Staringlizard/memwa2/hw/drivers/disp/disp.c

/*
 * memwa2 display driver
 *
 * Copyright (c) 2016 Mathias Edman <mail@dicetec.com>
 *
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
 */


/**
 * This driver handles all graphics and configuration.
 */

#include "disp.h"
#include "stm32f7xx_hal_ltdc.h"
#include "stm32f7xx_hal_dma2d.h"
#include <string.h>

#define VGA_WIDTH  ((uint16_t)640)
#define VGA_HEIGHT ((uint16_t)480)
#define VGA_HSYNC  ((uint16_t)96)
#define VGA_HBP    ((uint16_t)48)
#define VGA_HFP    ((uint16_t)16)
#define VGA_VSYNC  ((uint16_t)2)
#define VGA_VBP    ((uint16_t)31)
#define VGA_VFP    ((uint16_t)11)

#define SVGA_WIDTH  ((uint16_t)800)
#define SVGA_HEIGHT ((uint16_t)600)
#define SVGA_HSYNC  ((uint16_t)128)
#define SVGA_HBP    ((uint16_t)88)
#define SVGA_HFP    ((uint16_t)40)
#define SVGA_VSYNC  ((uint16_t)4)
#define SVGA_VBP    ((uint16_t)23)
#define SVGA_VFP    ((uint16_t)1)

#define DISP_MAIN_LAYER       0
#define DISP_EMU_LAYER        1

#define CLUT_TEXT_BG_POS      16
#define CLUT_TEXT_FG_POS      17
#define CLUT_MARKER_POS       18
#define CLUT_MAX              19

LTDC_HandleTypeDef g_ltdc_handle; /* used by irq.c */
static LTDC_LayerCfgTypeDef g_ltdc_layer_cfg_a[2];
static uint32_t g_memory_addr_a[3];

static uint32_t clut_a[CLUT_MAX] =
{
    0x000000, /* black */
    0xFFFFFF, /* white */
    0x744335, /* red */
    0x7CACBA, /* cyan */
    0x7B4890, /* violet */
    0x64974F, /* green */
    0x403285, /* blue */
    0xBFCD7A, /* yellow */
    0x7B5B2F, /* orange */
    0x4f4500, /* brown */
    0xa37265, /* light red */
    0x505050, /* grey 1 */
    0x787878, /* grey 2 */
    0xa4d78e, /* light green */
    0x786abd, /* light blue */
    0x9f9f9f, /* grey 3 */
    0x010211, /* text background */
    0x8f9fed, /* text forground */
    0x151bfb, /* marker */
};

void disp_init(disp_mode_t disp_mode)
{
    switch(disp_mode)
    {
        case DISP_MODE_VGA:
            /* Timing configuration */
            g_ltdc_handle.Init.HorizontalSync = (VGA_HSYNC - 1);
            g_ltdc_handle.Init.VerticalSync = (VGA_VSYNC - 1);
            g_ltdc_handle.Init.AccumulatedHBP = (VGA_HSYNC + VGA_HBP - 1);
            g_ltdc_handle.Init.AccumulatedVBP = (VGA_VSYNC + VGA_VBP - 1);  
            g_ltdc_handle.Init.AccumulatedActiveH = (VGA_HEIGHT + VGA_VSYNC + VGA_VBP - 1);
            g_ltdc_handle.Init.AccumulatedActiveW = (VGA_WIDTH + VGA_HSYNC + VGA_HBP - 1);
            g_ltdc_handle.Init.TotalHeigh = (VGA_HEIGHT + VGA_VSYNC + VGA_VBP + VGA_VFP - 1);
            g_ltdc_handle.Init.TotalWidth = (VGA_WIDTH + VGA_HSYNC + VGA_HBP + VGA_HFP - 1);

            /* Background value */
            g_ltdc_handle.Init.Backcolor.Blue = 0;
            g_ltdc_handle.Init.Backcolor.Green = 0;
            g_ltdc_handle.Init.Backcolor.Red = 0;

            /* Polarity */
            g_ltdc_handle.Init.HSPolarity = LTDC_HSPOLARITY_AL;
            g_ltdc_handle.Init.VSPolarity = LTDC_VSPOLARITY_AL; 
            g_ltdc_handle.Init.DEPolarity = LTDC_DEPOLARITY_AL;  
            g_ltdc_handle.Init.PCPolarity = LTDC_PCPOLARITY_IPC;
            g_ltdc_handle.Instance = LTDC;
            break;
        case DISP_MODE_SVGA:
            /* Timing configuration */
            g_ltdc_handle.Init.HorizontalSync = (SVGA_HSYNC - 1);
            g_ltdc_handle.Init.VerticalSync = (SVGA_VSYNC - 1);
            g_ltdc_handle.Init.AccumulatedHBP = (SVGA_HSYNC + SVGA_HBP - 1);
            g_ltdc_handle.Init.AccumulatedVBP = (SVGA_VSYNC + SVGA_VBP - 1);  
            g_ltdc_handle.Init.AccumulatedActiveH = (SVGA_HEIGHT + SVGA_VSYNC + SVGA_VBP - 1);
            g_ltdc_handle.Init.AccumulatedActiveW = (SVGA_WIDTH + SVGA_HSYNC + SVGA_HBP - 1);
            g_ltdc_handle.Init.TotalHeigh = (SVGA_HEIGHT + SVGA_VSYNC + SVGA_VBP + SVGA_VFP - 1);
            g_ltdc_handle.Init.TotalWidth = (SVGA_WIDTH + SVGA_HSYNC + SVGA_HBP + SVGA_HFP - 1); 

            /* Background value */
            g_ltdc_handle.Init.Backcolor.Blue = 0;
            g_ltdc_handle.Init.Backcolor.Green = 0;
            g_ltdc_handle.Init.Backcolor.Red = 0;

            /* Polarity */
            g_ltdc_handle.Init.HSPolarity = LTDC_HSPOLARITY_AL;
            g_ltdc_handle.Init.VSPolarity = LTDC_VSPOLARITY_AL; 
            g_ltdc_handle.Init.DEPolarity = LTDC_DEPOLARITY_AL;  
            g_ltdc_handle.Init.PCPolarity = LTDC_PCPOLARITY_IIPC;
            g_ltdc_handle.Instance = LTDC;
    }

    HAL_LTDC_Init(&g_ltdc_handle);

    HAL_LTDC_ConfigCLUT(&g_ltdc_handle, clut_a, CLUT_MAX, 0);
    HAL_LTDC_ConfigCLUT(&g_ltdc_handle, clut_a, CLUT_MAX, 1);

    HAL_LTDC_EnableCLUT(&g_ltdc_handle, 0);
    HAL_LTDC_EnableCLUT(&g_ltdc_handle, 1);

    HAL_LTDC_ProgramLineEvent(&g_ltdc_handle, 200);
    __HAL_LTDC_DISABLE_IT(&g_ltdc_handle, LTDC_IT_LI); /* Disable line events for now */
}

void *disp_get_layer(uint8_t layer)
{
    return (void *)(g_ltdc_handle.LayerCfg[layer].FBStartAdress);
}

void disp_set_memory(uint8_t layer, uint32_t memory)
{
    g_memory_addr_a[layer] = memory;
}

void disp_set_layer(uint8_t layer,
                    uint32_t window_x0,
                    uint32_t window_x1,
                    uint32_t window_y0,
                    uint32_t window_y1,
                    uint32_t buffer_x,
                    uint32_t buffer_y,
                    uint8_t alpha,
                    uint32_t pixel_format)
{
    /* Layer Init */
    g_ltdc_layer_cfg_a[layer].WindowX0 = window_x0;
    g_ltdc_layer_cfg_a[layer].WindowX1 = window_x1;
    g_ltdc_layer_cfg_a[layer].WindowY0 = window_y0;
    g_ltdc_layer_cfg_a[layer].WindowY1 = window_y1;
    g_ltdc_layer_cfg_a[layer].Alpha = alpha;
    g_ltdc_layer_cfg_a[layer].Alpha0 = 0;
    g_ltdc_layer_cfg_a[layer].Backcolor.Blue = 0;
    g_ltdc_layer_cfg_a[layer].Backcolor.Green = 0;
    g_ltdc_layer_cfg_a[layer].Backcolor.Red = 0;
    g_ltdc_layer_cfg_a[layer].BlendingFactor1 = LTDC_BLENDING_FACTOR1_PAxCA;
    g_ltdc_layer_cfg_a[layer].BlendingFactor2 = LTDC_BLENDING_FACTOR2_PAxCA;
    g_ltdc_layer_cfg_a[layer].ImageWidth = buffer_x;
    g_ltdc_layer_cfg_a[layer].ImageHeight = buffer_y;
    g_ltdc_layer_cfg_a[layer].PixelFormat = pixel_format;
    g_ltdc_layer_cfg_a[layer].FBStartAdress = g_memory_addr_a[layer];

    HAL_LTDC_ConfigLayer(&g_ltdc_handle, &g_ltdc_layer_cfg_a[layer], layer);
}

void disp_activate_layer(uint8_t layer)
{
    __HAL_LTDC_LAYER_ENABLE(&g_ltdc_handle, layer);
    __HAL_LTDC_RELOAD_CONFIG(&g_ltdc_handle);
}

void disp_deactivate_layer(uint8_t layer)
{
    __HAL_LTDC_LAYER_DISABLE(&g_ltdc_handle, layer);
    __HAL_LTDC_RELOAD_CONFIG(&g_ltdc_handle);
}

void disp_fill_layer(uint8_t layer, uint32_t color)
{
    uint32_t i;

    for(i = 0; i < g_ltdc_layer_cfg_a[layer].ImageWidth * g_ltdc_layer_cfg_a[layer].ImageHeight; i++)
    {
        if(g_ltdc_layer_cfg_a[layer].PixelFormat == LTDC_PIXEL_FORMAT_L8)
        {
            *((uint8_t *)g_ltdc_layer_cfg_a[layer].FBStartAdress + i) = color;
        }
        else if(g_ltdc_layer_cfg_a[layer].PixelFormat == LTDC_PIXEL_FORMAT_RGB565)
        {
            *((uint16_t *)g_ltdc_layer_cfg_a[layer].FBStartAdress + i) = color;
        }
        else if(g_ltdc_layer_cfg_a[layer].PixelFormat == LTDC_PIXEL_FORMAT_ARGB8888)
        {
            *((uint32_t *)g_ltdc_layer_cfg_a[layer].FBStartAdress + i) = color;
        }
    }
}

void disp_move_layer(uint8_t layer, uint32_t x, uint32_t y)
{
    HAL_LTDC_SetWindowPosition(&g_ltdc_handle, x, y, layer);
}

void disp_flip_buffer(uint8_t **done_buffer_pp)
{
    /* Set layer to be displayed */
    HAL_LTDC_SetAddress(&g_ltdc_handle, (uint32_t)*done_buffer_pp, DISP_EMU_LAYER);

    /* And shift buffer */
    if((uint32_t)*done_buffer_pp == g_memory_addr_a[MEM_ADDR_BUFFER1])
    {
        *done_buffer_pp = (uint8_t *)g_memory_addr_a[MEM_ADDR_BUFFER2];
    }
    else
    {
        *done_buffer_pp = (uint8_t *)g_memory_addr_a[MEM_ADDR_BUFFER1];
    }
}

void disp_set_clut_table(uint32_t *clut_p)
{
    memcpy(clut_a, clut_p, CLUT_MAX * sizeof(uint32_t));
    HAL_LTDC_ConfigCLUT(&g_ltdc_handle, clut_a, CLUT_MAX, 0);
    HAL_LTDC_ConfigCLUT(&g_ltdc_handle, clut_a, CLUT_MAX, 1);
}

void disp_enable_clut(uint8_t layer)
{
    HAL_LTDC_EnableCLUT(&g_ltdc_handle, layer);
}

void disp_disable_clut(uint8_t layer)
{
    HAL_LTDC_DisableCLUT(&g_ltdc_handle, layer);
}

void HAL_LTDC_ErrorCallback(LTDC_HandleTypeDef *hltdc)
{
    main_warning("HAL LTDC error!", __FILE__, __LINE__, (uint32_t)hltdc->ErrorCode);
    __HAL_LTDC_ENABLE_IT(hltdc, LTDC_IT_TE);
    __HAL_LTDC_ENABLE_IT(hltdc, LTDC_IT_FU);
    hltdc->State = HAL_LTDC_STATE_READY;
    hltdc->ErrorCode = HAL_LTDC_ERROR_NONE;
}

void HAL_LTDC_LineEvenCallback(LTDC_HandleTypeDef *hltdc)
{
    main_error("HAL LTDC line callback!", __FILE__, __LINE__, (uint32_t)hltdc->ErrorCode);
    //HAL_LTDC_ProgramLineEvent(hltdc, 200);
}
