Staringlizard/memwa2/hw/irq/irq.c

/**
  ******************************************************************************
  * @file    FatFs/FatFs_uSD/Src/stm32f7xx_it.c
  * @author  MCD Application Team
  * @version V1.0.2
  * @date    18-November-2015 
  * @brief   Main Interrupt Service Routines.
  *          This file provides template for all exceptions handler and
  *          peripherals interrupt service routine.
  ******************************************************************************
  * @attention
  *
  * <h2><center>&copy; COPYRIGHT(c) 2015 STMicroelectronics</center></h2>
  *
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
  ******************************************************************************
  */

/* Includes ------------------------------------------------------------------*/
#include "irq.h"
#include "config.h"
#include "usbd_cdc_if.h"
#include "sidbus.h"
#include "joyst.h"
#include "timer.h"
#include "adv7511.h"

/* Private typedef -----------------------------------------------------------*/
/* Private define ------------------------------------------------------------*/
/* Private macro -------------------------------------------------------------*/
/* Private variables ---------------------------------------------------------*/
/* Private function prototypes -----------------------------------------------*/
/* Private functions ---------------------------------------------------------*/

extern HCD_HandleTypeDef hhcd;
extern PCD_HandleTypeDef hpcd;
extern PCD_HandleTypeDef hpcd;
extern LTDC_HandleTypeDef g_ltdc_handle;

/******************************************************************************/
/*            Cortex-M7 Processor Exceptions Handlers                         */
/******************************************************************************/

/**
  * @brief  This function handles NMI exception.
  * @param  None
  * @retval None
  */
void NMI_Handler(void)
{
}

/**
  * @brief  This function handles Hard Fault exception.
  * @param  None
  * @retval None
  */
void HardFault_Handler(void)
{
  /* Go to infinite loop when Hard Fault exception occurs */
  while (1)
  {
  }
}

/**
  * @brief  This function handles Memory Manage exception.
  * @param  None
  * @retval None
  */
void MemManage_Handler(void)
{
  /* Go to infinite loop when Memory Manage exception occurs */
  while (1)
  {
  }
}

/**
  * @brief  This function handles Bus Fault exception.
  * @param  None
  * @retval None
  */
void BusFault_Handler(void)
{
  /* Go to infinite loop when Bus Fault exception occurs */
  while (1)
  {
  }
}

/**
  * @brief  This function handles Usage Fault exception.
  * @param  None
  * @retval None
  */
void UsageFault_Handler(void)
{
  /* Go to infinite loop when Usage Fault exception occurs */
  while (1)
  {
  }
}

/**
  * @brief  This function handles SVCall exception.
  * @param  None
  * @retval None
  */
void SVC_Handler(void)
{
}

/**
  * @brief  This function handles Debug Monitor exception.
  * @param  None
  * @retval None
  */
void DebugMon_Handler(void)
{
}

/**
  * @brief  This function handles PendSVC exception.
  * @param  None
  * @retval None
  */
void PendSV_Handler(void)
{
}

/**
  * @brief  This function handles SysTick Handler.
  * @param  None
  * @retval None
  */
void SysTick_Handler(void)
{
  HAL_IncTick();
  systimer_tick();
}

void TIM3_IRQHandler(void)
{
  timer3_tick();
}

void LTDC_IRQHandler(void)
{
  HAL_LTDC_IRQHandler(&g_ltdc_handle);
}

void LTDC_ER_IRQHandler(void)
{
  HAL_LTDC_IRQHandler(&g_ltdc_handle);
}

/**
  * @brief  This function handles DMA2 Stream 3 interrupt request.
  * @param  None
  * @retval None
  */
void DMA2_Stream3_IRQHandler(void)
{
  ;//SD_DMA_Rx_IRQHandler();
}

/**
  * @brief  This function handles DMA2 Stream 6 interrupt request.
  * @param  None
  * @retval None
  */
void DMA2_Stream6_IRQHandler(void)
{
  ;//SD_DMA_Tx_IRQHandler(); 
}

/**
  * @brief  This function handles SDIO interrupt request.
  * @param  None
  * @retval None
  */
void SDMMC1_IRQHandler(void)
{
  ;//SD_IRQHandler();
}

/**
  * @brief  This function handles PPP interrupt request.
  * @param  None
  * @retval None
  */
/*void PPP_IRQHandler(void)
{
}*/

/**
  * @brief  This function handles USB-On-The-Go FS/HS global interrupt request.
  * @param  None
  * @retval None
  */
void OTG_FS_IRQHandler(void)
{
  HAL_PCD_IRQHandler(&hpcd);

  /* Flush the outgoing printf data */
  CDC_Itf_Flush();
}

/**
  * @brief  This function handles USB-On-The-Go FS/HS global interrupt request.
  * @param  None
  * @retval None
  */
void OTG_HS_IRQHandler(void)
{
  HAL_HCD_IRQHandler(&hhcd);

  /* Flush the outgoing printf data */
  CDC_Itf_Flush();
}

void EXTI2_IRQHandler(void)
{
  __HAL_GPIO_EXTI_CLEAR_FLAG(GPIO_PIN_2);
  if((GPIOE->IDR & GPIO_PIN_2) != (uint32_t)GPIO_PIN_RESET)
  {
    joyst_irq(JOYST_PORT_A, JOYST_ACTION_UP, JOYST_ACTION_STATE_RELEASED);
  }
  else
  {
    joyst_irq(JOYST_PORT_A, JOYST_ACTION_UP, JOYST_ACTION_STATE_PRESSED);
  }
}

void EXTI3_IRQHandler(void)
{
  __HAL_GPIO_EXTI_CLEAR_FLAG(GPIO_PIN_3);
  if((GPIOE->IDR & GPIO_PIN_3) != (uint32_t)GPIO_PIN_RESET)
  {
    joyst_irq(JOYST_PORT_A, JOYST_ACTION_DOWN, JOYST_ACTION_STATE_RELEASED);
  }
  else
  {
    joyst_irq(JOYST_PORT_A, JOYST_ACTION_DOWN, JOYST_ACTION_STATE_PRESSED);
  }
}

void EXTI4_IRQHandler(void)
{
  __HAL_GPIO_EXTI_CLEAR_FLAG(GPIO_PIN_4);
  if((GPIOH->IDR & GPIO_PIN_4) != (uint32_t)GPIO_PIN_RESET)
  {
    joyst_irq(JOYST_PORT_B, JOYST_ACTION_FIRE, JOYST_ACTION_STATE_RELEASED);
  }
  else
  {
    joyst_irq(JOYST_PORT_B, JOYST_ACTION_FIRE, JOYST_ACTION_STATE_PRESSED);
  }
}

void EXTI9_5_IRQHandler(void)
{
  if(__HAL_GPIO_EXTI_GET_IT(GPIO_PIN_5) != RESET)
  {
    __HAL_GPIO_EXTI_CLEAR_FLAG(GPIO_PIN_5);
    if((GPIOB->IDR & GPIO_PIN_5) != (uint32_t)GPIO_PIN_RESET)
    {
      joyst_irq(JOYST_PORT_A, JOYST_ACTION_LEFT, JOYST_ACTION_STATE_RELEASED);
    }
    else
    {
      joyst_irq(JOYST_PORT_A, JOYST_ACTION_LEFT, JOYST_ACTION_STATE_PRESSED);
    }
  }
  else if(__HAL_GPIO_EXTI_GET_IT(GPIO_PIN_6) != RESET)
  {
    __HAL_GPIO_EXTI_CLEAR_FLAG(GPIO_PIN_6);
    if((GPIOF->IDR & GPIO_PIN_6) != (uint32_t)GPIO_PIN_RESET)
    {
      joyst_irq(JOYST_PORT_B, JOYST_ACTION_LEFT, JOYST_ACTION_STATE_RELEASED);
    }
    else
    {
      joyst_irq(JOYST_PORT_B, JOYST_ACTION_LEFT, JOYST_ACTION_STATE_PRESSED);
    }
  }
  else if(__HAL_GPIO_EXTI_GET_IT(GPIO_PIN_7) != RESET)
  {
    __HAL_GPIO_EXTI_CLEAR_FLAG(GPIO_PIN_7);
    if((GPIOF->IDR & GPIO_PIN_7) != (uint32_t)GPIO_PIN_RESET)
    {
      joyst_irq(JOYST_PORT_B, JOYST_ACTION_RIGHT, JOYST_ACTION_STATE_RELEASED);
    }
    else
    {
      joyst_irq(JOYST_PORT_B, JOYST_ACTION_RIGHT, JOYST_ACTION_STATE_PRESSED);
    }
  }
  else if(__HAL_GPIO_EXTI_GET_IT(GPIO_PIN_8) != RESET)
  {
    __HAL_GPIO_EXTI_CLEAR_FLAG(GPIO_PIN_8);
    if((GPIOF->IDR & GPIO_PIN_8) != (uint32_t)GPIO_PIN_RESET)
    {
      joyst_irq(JOYST_PORT_B, JOYST_ACTION_UP, JOYST_ACTION_STATE_RELEASED);
    }
    else
    {
      joyst_irq(JOYST_PORT_B, JOYST_ACTION_UP, JOYST_ACTION_STATE_PRESSED);
    }
  }
  else if(__HAL_GPIO_EXTI_GET_IT(GPIO_PIN_9) != RESET)
  {
    __HAL_GPIO_EXTI_CLEAR_FLAG(GPIO_PIN_9);
    if((GPIOF->IDR & GPIO_PIN_9) != (uint32_t)GPIO_PIN_RESET)
    {
      joyst_irq(JOYST_PORT_B, JOYST_ACTION_DOWN, JOYST_ACTION_STATE_RELEASED);
    }
    else
    {
      joyst_irq(JOYST_PORT_B, JOYST_ACTION_DOWN, JOYST_ACTION_STATE_PRESSED);
    }
  }  
}

void EXTI15_10_IRQHandler(void)
{
  if(__HAL_GPIO_EXTI_GET_IT(GPIO_PIN_13) != RESET)
  {
    __HAL_GPIO_EXTI_CLEAR_FLAG(GPIO_PIN_13);
    sidbus_irq();
  }
  else if(__HAL_GPIO_EXTI_GET_IT(GPIO_PIN_10) != RESET)
  {
    __HAL_GPIO_EXTI_CLEAR_FLAG(GPIO_PIN_10);
    if((GPIOA->IDR & GPIO_PIN_10) != (uint32_t)GPIO_PIN_RESET)
    {
      joyst_irq(JOYST_PORT_A, JOYST_ACTION_FIRE, JOYST_ACTION_STATE_RELEASED);
    }
    else
    {
      joyst_irq(JOYST_PORT_A, JOYST_ACTION_FIRE, JOYST_ACTION_STATE_PRESSED);
    }
  }
  else if(__HAL_GPIO_EXTI_GET_IT(GPIO_PIN_14) != RESET)
  {
    __HAL_GPIO_EXTI_CLEAR_FLAG(GPIO_PIN_14);
    if((GPIOG->IDR & GPIO_PIN_14) != (uint32_t)GPIO_PIN_RESET)
    {
      joyst_irq(JOYST_PORT_A, JOYST_ACTION_RIGHT, JOYST_ACTION_STATE_RELEASED);
    }
    else
    {
      joyst_irq(JOYST_PORT_A, JOYST_ACTION_RIGHT, JOYST_ACTION_STATE_PRESSED);
    }
  }
  else if(__HAL_GPIO_EXTI_GET_IT(GPIO_PIN_15) != RESET)
  {
    __HAL_GPIO_EXTI_CLEAR_FLAG(GPIO_PIN_15);
    adv7511_irq();
  }
}

/* This can be found in disp.c */
/*void HAL_LTDC_ErrorCallback(LTDC_HandleTypeDef *hltdc)
{

}*/

/************************ (C) COPYRIGHT STMicroelectronics *****END OF FILE****/
