Staringlizard/memwa2/hw/drivers/sdcard/diskio.c

/*-----------------------------------------------------------------------*/
/* Low level disk I/O module skeleton for FatFs     (C)ChaN, 2014        */
/*                                                                       */
/*   Portions COPYRIGHT 2015 STMicroelectronics                          */
/*   Portions Copyright (C) 2014, ChaN, all right reserved               */
/*-----------------------------------------------------------------------*/
/* If a working storage control module is available, it should be        */
/* attached to the FatFs via a glue function rather than modifying it.   */
/* This is an example of glue functions to attach various exsisting      */
/* storage control modules to the FatFs module with a defined API.       */
/*-----------------------------------------------------------------------*/

/**
  ******************************************************************************
  * @file    diskio.c 
  * @author  MCD Application Team
  * @version V1.3.0
  * @date    08-May-2015
  * @brief   FatFs low level disk I/O module.
  ******************************************************************************
  * @attention
  *
  * Licensed under MCD-ST Liberty SW License Agreement V2, (the "License");
  * You may not use this file except in compliance with the License.
  * You may obtain a copy of the License at:
  *
  *        http://www.st.com/software_license_agreement_liberty_v2
  *
  * Unless required by applicable law or agreed to in writing, software 
  * distributed under the License is distributed on an "AS IS" BASIS, 
  * WITHOUT WARRANTIES OR CONDITIONS OF ANY KIND, either express or implied.
  * See the License for the specific language governing permissions and
  * limitations under the License.
  *
  ******************************************************************************
  */

/* Includes ------------------------------------------------------------------*/
#include "diskio.h"
#include "config.h"
#include "stm32f7xx_hal_dma.h"
#include "stm32f7xx_hal_sd.h"

#define BLOCK_SIZE     512
static uint8_t initialized;

extern SD_HandleTypeDef g_sd_handle;

/**
  * @brief  Gets Disk Status 
  * @param  pdrv: Physical drive number (0..)
  * @retval DSTATUS: Operation status
  */
DSTATUS disk_status(BYTE pdrv)
{
  DSTATUS stat = RES_OK;
  return stat;
}

/**
  * @brief  Initializes a Drive
  * @param  pdrv: Physical drive number (0..)
  * @retval DSTATUS: Operation status
  */
DSTATUS disk_initialize(BYTE pdrv)
{
  DSTATUS stat = RES_OK;
  initialized = 1;
  return stat;
}

/**
  * @brief  Reads Sector(s) 
  * @param  pdrv: Physical drive number (0..)
  * @param  *buff: Data buffer to store read data
  * @param  sector: Sector address (LBA)
  * @param  count: Number of sectors to read (1..128)
  * @retval DRESULT: Operation result
  */
DRESULT disk_read (
	BYTE pdrv,		/* Physical drive nmuber to identify the drive */
	BYTE *buff,		/* Data buffer to store read data */
	DWORD sector,	/* Sector address in LBA */
	UINT count		/* Number of sectors to read */
)
{
  HAL_SD_ErrorTypedef hal_sd_res = SD_OK;
  DRESULT res = RES_OK;

  hal_sd_res = HAL_SD_ReadBlocks(&g_sd_handle, (uint32_t *)buff, (uint32_t)(sector), BLOCK_SIZE, count);

  if(hal_sd_res != SD_OK)
  {
      res = RES_ERROR;
  }

  return res;
}

/**
  * @brief  Writes Sector(s)  
  * @param  pdrv: Physical drive number (0..)
  * @param  *buff: Data to be written
  * @param  sector: Sector address (LBA)
  * @param  count: Number of sectors to write (1..128)
  * @retval DRESULT: Operation result
  */
#if _USE_WRITE == 1
DRESULT disk_write (
	BYTE pdrv,		/* Physical drive nmuber to identify the drive */
	const BYTE *buff,	/* Data to be written */
	DWORD sector,		/* Sector address in LBA */
	UINT count        	/* Number of sectors to write */
)
{
  HAL_SD_ErrorTypedef hal_sd_res = SD_OK;
  DRESULT res = RES_OK;

  hal_sd_res = HAL_SD_WriteBlocks(&g_sd_handle, (uint32_t *)buff, (uint32_t)(sector), BLOCK_SIZE, count);

  if(hal_sd_res != SD_OK)
  {
      res = RES_ERROR;
  }

  return res;
}
#endif /* _USE_WRITE == 1 */

/**
  * @brief  I/O control operation  
  * @param  pdrv: Physical drive number (0..)
  * @param  cmd: Control code
  * @param  *buff: Buffer to send/receive control data
  * @retval DRESULT: Operation result
  */
#if _USE_IOCTL == 1
DRESULT disk_ioctl (
	BYTE pdrv,		/* Physical drive nmuber (0..) */
	BYTE cmd,		/* Control code */
	void *buff		/* Buffer to send/receive control data */
)
{
  DRESULT res = RES_OK;

  HAL_SD_CardInfoTypedef HAL_SD_CardInfoType;
  
  if(!initialized)
  {
    return RES_NOTRDY;
  }
  
  switch (cmd)
  {
  /* Make sure that no pending write process */
  case CTRL_SYNC :
    res = RES_OK;
    break;
  
  /* Get number of sectors on the disk (DWORD) */
  case GET_SECTOR_COUNT:
    HAL_SD_Get_CardInfo(&g_sd_handle, &HAL_SD_CardInfoType);
    *(DWORD*)buff = HAL_SD_CardInfoType.CardCapacity / BLOCK_SIZE;
    res = RES_OK;
    break;
  
  /* Get R/W sector size (WORD) */
  case GET_SECTOR_SIZE :
    *(WORD*)buff = BLOCK_SIZE;
    res = RES_OK;
    break;
  
  /* Get erase block size in unit of sector (DWORD) */
  case GET_BLOCK_SIZE :
    *(DWORD*)buff = BLOCK_SIZE;
    break;
  
  default:
    res = RES_PARERR;
  }

  return res;
}
#endif /* _USE_IOCTL == 1 */

/**
  * @brief  Gets Time from RTC 
  * @param  None
  * @retval Time in DWORD
  */
DWORD get_fattime (void)
{
  return 0;
}

/************************ (C) COPYRIGHT STMicroelectronics *****END OF FILE****/
