Staringlizard/memwa2/hw/util/console/console.c

/*
 * memwa2 console utility
 *
 * Copyright (c) 2016 Mathias Edman <mail@dicetec.com>
 *
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
 */


/**
 * This utility is resposible for the console that is available
 * from usb cable. It handles incoming commands and also outgoing
 * prints from whole software. This file implements the printf
 * function.
 */

#include "console.h"
#include "adv7511.h"
#include "usbd_core.h"
#include "usbd_cdc.h"
#include "usbd_cdc_if.h"
#include <string.h>

#define STDOUT_FILENO 	1
#define STDERR_FILENO 	2

#define IPSR_THREADED_MODE      0x01

USBD_HandleTypeDef g_usbd_device;
extern USBD_DescriptorsTypeDef VCP_Desc;
extern USBD_CDC_ItfTypeDef  USBD_CDC_fops;

typedef enum
{
    CMD_I2C_READ,
    CMD_I2C_WRITE,
    CMD_MEM_READ,
    CMD_MEM_WRITE,
    CMD_MAX
} cmd_t;

static char *g_cmd_list_ap[5] = {"i2c_read", "i2c_write", "mem_read", "mem_write", NULL};

static char *g_console_help_p =   "[i2c_read <reg>], read adv7511 register\r" \
                                "[i2c_write <reg> <val>], write adv7511 register\r" \
                                "[mem_read <addr>], read memory address\r" \
                                "[mem_write <addr> <val>], write to memory address\n";
static uint8_t g_cmd_input_str_a[128] = "";
static uint8_t g_cmd_input_cnt = 0;
static char g_delimiter_a[2] = " ";

static uint32_t console_atoi(char *str_p)
{
    if(str_p[1] == 'x')
    {
        return strtoul(str_p, NULL, 16);
    }
    else
    {
        return atoi(str_p);
    }
}

static void console_interpret(uint8_t *buf, uint32_t len)
{
    char *argsv_pp[16];
    uint8_t argsc = 0;
    uint8_t i;
    cmd_t cmd = CMD_MAX;

    memset(argsv_pp, 0x00, 16 * sizeof(char *));

    argsv_pp[argsc] = strtok((char *)buf, g_delimiter_a);
    argsc++;
    while(argsv_pp[argsc-1] != NULL)
    {
        argsv_pp[argsc] = strtok(NULL, g_delimiter_a);
        argsc++;
    }

    for(i = 0; i < CMD_MAX; i++)
    {
        if(strcmp(argsv_pp[0], g_cmd_list_ap[i]) == 0)
        {
            cmd = (cmd_t)i;
            break;
        }
    }

    switch(cmd)
    {
        case CMD_I2C_READ:
        {
            uint8_t reg;
            uint8_t val;
            if(argsv_pp[1] == NULL)
            {
                printf("need one argument!\n");
                break;
            }
            reg = console_atoi(argsv_pp[1]);
            val = adv7511_rd_reg(reg);
            printf("reading 0x%02X from register 0x%02X\n", val, reg);
        }
        break;
        case CMD_I2C_WRITE:
        {
            uint8_t reg;
            uint8_t val;
            if(argsv_pp[1] == NULL || argsv_pp[2] == NULL)
            {
                printf("need two arguments!\n");
                break;
            }
            reg = console_atoi(argsv_pp[1]);
            val = console_atoi(argsv_pp[2]);
            adv7511_wr_reg(reg, val);
            printf("writing 0x%02X to register 0x%02X\n", val, reg);
        }
        break;
        case CMD_MEM_READ:
        {
            uint32_t addr;
            uint8_t val;
            if(argsv_pp[1] == NULL)
            {
                printf("need one argument!\n");
                break;
            }

            addr = console_atoi(argsv_pp[1]);
            val = *(uint8_t *)addr;
            printf("reading 0x%02X from address 0x%02X\n", val, (unsigned int)addr);
        }
        break;
        case CMD_MEM_WRITE:
        {
            uint32_t addr;
            uint8_t val;
            if(argsv_pp[1] == NULL || argsv_pp[2] == NULL)
            {
                printf("need two arguments!\n");
                break;
            }

            addr = console_atoi(argsv_pp[1]);
            val = console_atoi(argsv_pp[2]);
            *(uint8_t *)addr = val;
            printf("writing 0x%02X to address 0x%02X\n", val, (unsigned int)addr);
        }
        break;
    default:
        printf("%s", g_console_help_p);
    }
}

static void console_receive(uint8_t *buf, uint32_t len)
{
    uint8_t i;

    if((g_cmd_input_cnt + len) >= 128)
    {
        printf("console: command too long, buffer reset!\n");
        memset(g_cmd_input_str_a, 0x00, 128);
        g_cmd_input_cnt = 0;
        return;
    }

    memcpy(g_cmd_input_str_a + g_cmd_input_cnt, buf, len);

    g_cmd_input_cnt += len;

    for(i = 0; i < g_cmd_input_cnt; i++)
    {
        if(g_cmd_input_str_a[i] == '\r')
        {
            /* Send new line */
            CDC_Itf_Send((uint8_t *)"\n", 1);

            /* Remove CR and NL */
            while(g_cmd_input_str_a[g_cmd_input_cnt - 1] == '\n' ||
                  g_cmd_input_str_a[g_cmd_input_cnt - 1] == '\r')
            {
                g_cmd_input_str_a[g_cmd_input_cnt - 1] = '\0';
                g_cmd_input_cnt--;
            }

            /* Interpret the command */
            console_interpret(g_cmd_input_str_a, g_cmd_input_cnt);
            memset(g_cmd_input_str_a, 0x00, 128);
            g_cmd_input_cnt = 0;
            return;
        }
    }

    /* Remote echo */
    CDC_Itf_Send((uint8_t *)buf, len);
}

void console_init()
{
  /* Init Device Library */
  USBD_Init(&g_usbd_device, &VCP_Desc, 0);
  
  /* Add Supported Class */
  USBD_RegisterClass(&g_usbd_device, USBD_CDC_CLASS);
  
  /* Add CDC Interface Class */
  USBD_CDC_RegisterInterface(&g_usbd_device, &USBD_CDC_fops);
  
  /* Start Device Process */
  USBD_Start(&g_usbd_device);

  /* Register receive function */
  CDC_Iif_RegisterReceiveCb(console_receive);

  memset(g_cmd_input_str_a, 0x00, 128);
}

/* So that printf() will output on this device */
int _write(int file, char *ptr, int len)
{
    switch (file)
    {
    case STDOUT_FILENO: /*stdout*/
        CDC_Itf_Send((uint8_t *)ptr, (uint32_t)len);
        break;
    case STDERR_FILENO: /* stderr */
        CDC_Itf_Send((uint8_t *)ptr, (uint32_t)len);
        break;
    default:
        return -1;
    }

    /*
     * If thread mode the buffer can be flushed at any time.
     * This is not the case when in interrupt context, since
     * here only one flush can be done per IRQ.
     */
    if(__get_IPSR() & IPSR_THREADED_MODE)
    {
        CDC_Itf_Flush();
    }

    return len;
}
